svenpetersen1965/C64-Control-Port-Switch-Rapid-Fire-/case/rev 0/InkScape/decal.png

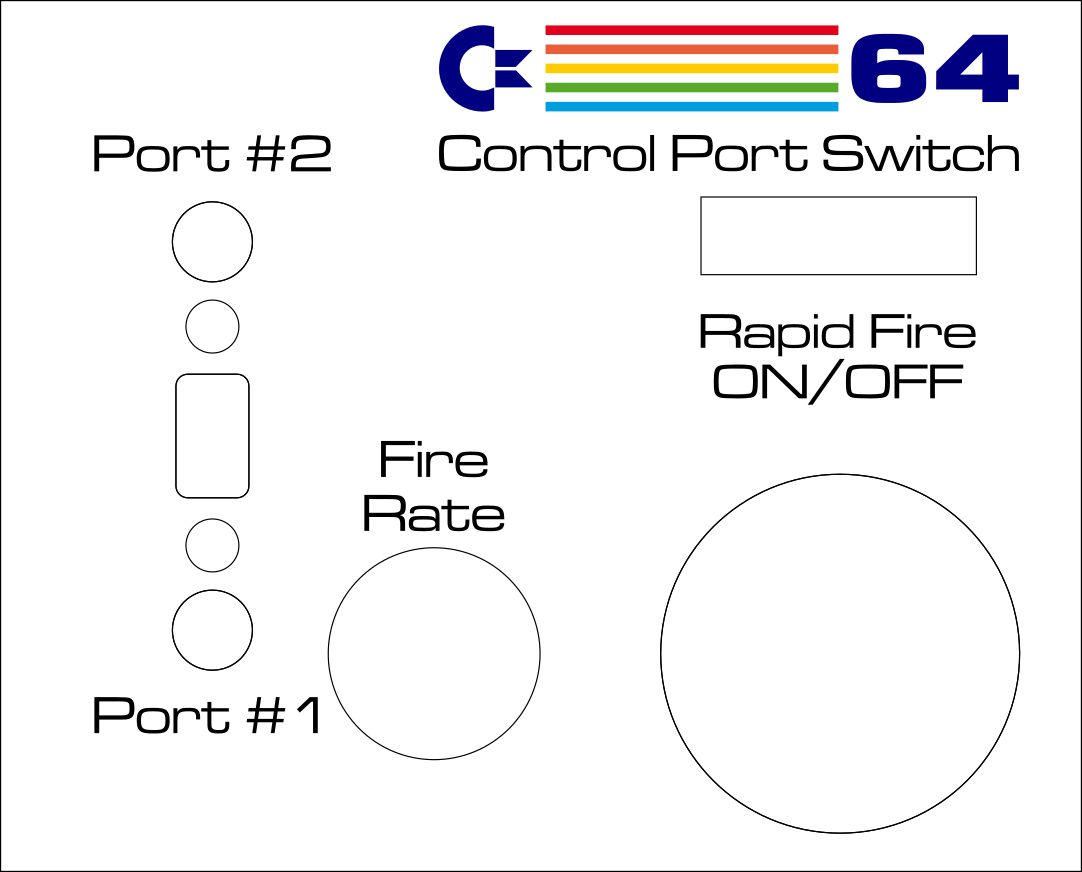
case/rev 0/InkScape/decal.png
