svenpetersen1965/C64-Control-Port-Switch-Rapid-Fire-/Hardware/Rev. 1/pictures/4124_-_display_cable.JPG

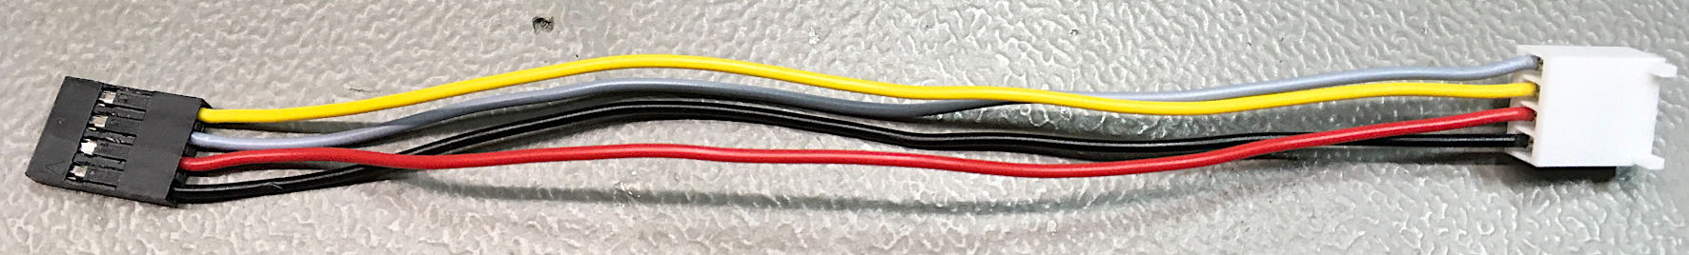
Hardware/Rev. 1/pictures/4124_-_display_cable.JPG
