svenpetersen1965/C64-Control-Port-Switch-Rapid-Fire-/Hardware/Rev. 1/pictures/4126_-_potentiometer_cable.JPG

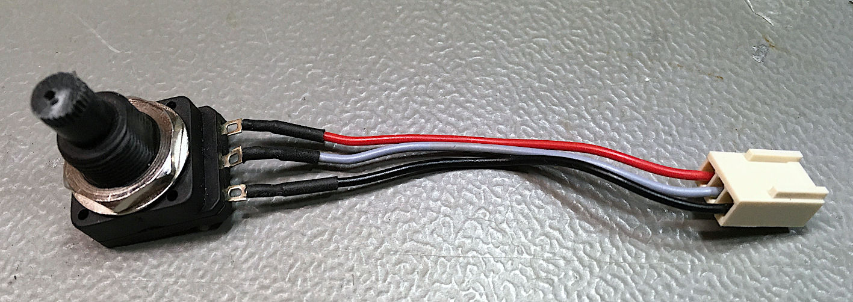
Hardware/Rev. 1/pictures/4126_-_potentiometer_cable.JPG
