svenpetersen1965/C64-Control-Port-Switch-Rapid-Fire-/Hardware/Rev. 1/pictures/4131_-_display.JPG

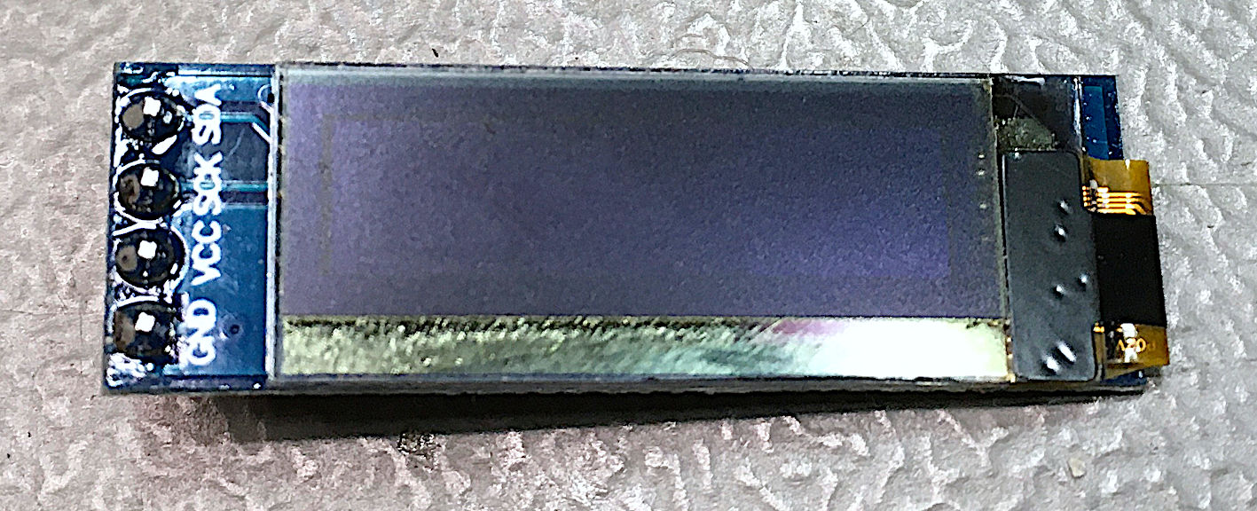
Hardware/Rev. 1/pictures/4131_-_display.JPG
