svenpetersen1965/C64-Control-Port-Switch-Rapid-Fire-/Hardware/Rev. 1/pictures/4147_-_wire_separated.JPG

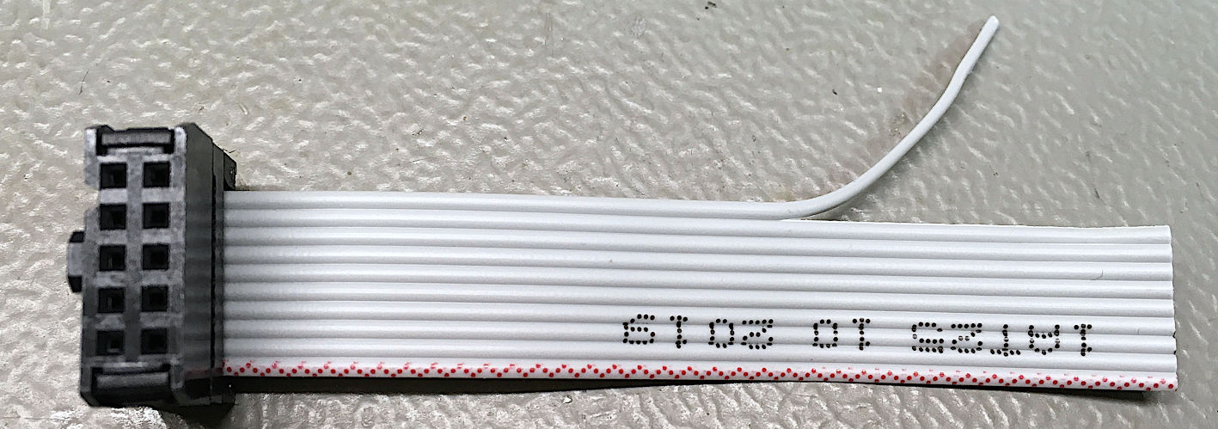
Hardware/Rev. 1/pictures/4147_-_wire_separated.JPG
