svenpetersen1965/C64-Control-Port-Switch-Rapid-Fire-/Hardware/Rev. 1/pictures/4148_-_Dsub_aligned.JPG

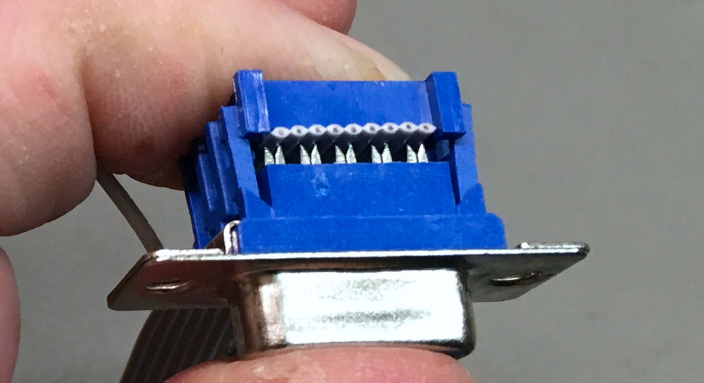
Hardware/Rev. 1/pictures/4148_-_Dsub_aligned.JPG
