svenpetersen1965/C64-Control-Port-Switch-Rapid-Fire-/Hardware/Rev. 1/pictures/4149_-_Dsub_wrench.JPG

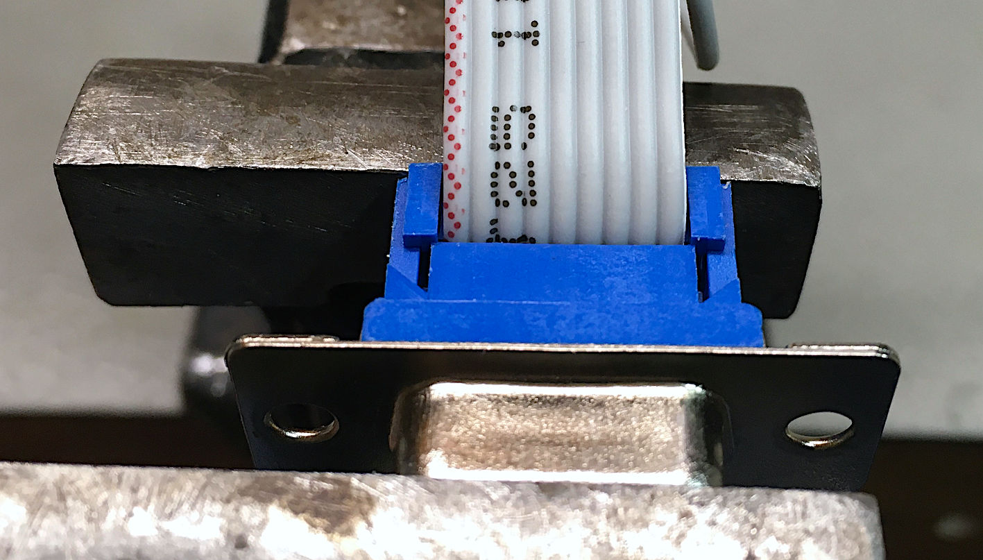
Hardware/Rev. 1/pictures/4149_-_Dsub_wrench.JPG
