svenpetersen1965/C64-Control-Port-Switch-Rapid-Fire-/Hardware/Rev. 1/pictures/ada_gfx.png

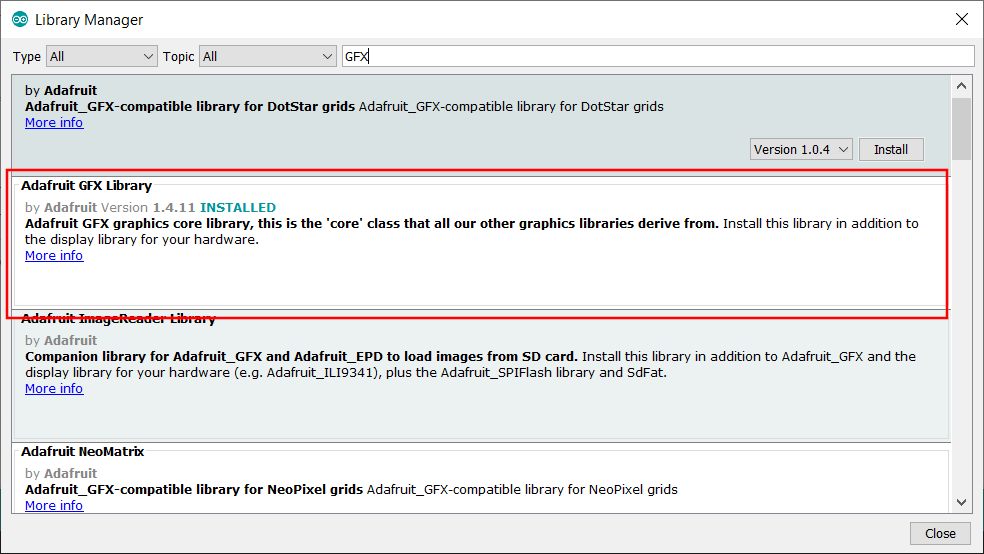
Hardware/Rev. 1/pictures/ada_gfx.png
