svenpetersen1965/C64-Control-Port-Switch-Rapid-Fire-/Hardware/Rev. 1/pictures/JSRF_+slope_out_100us.png

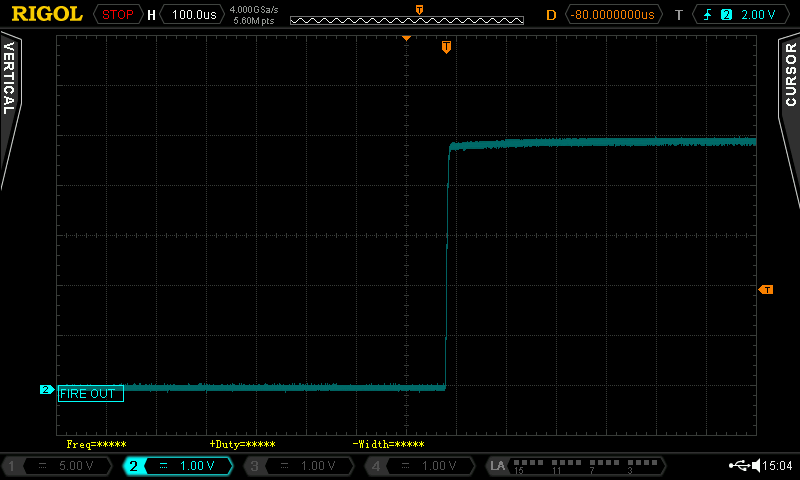
Hardware/Rev. 1/pictures/JSRF_+slope_out_100us.png
