svenpetersen1965/C64-Control-Port-Switch-Rapid-Fire-/Hardware/Rev. 1/pictures/JSRF_-slope_in_out_1ms.png

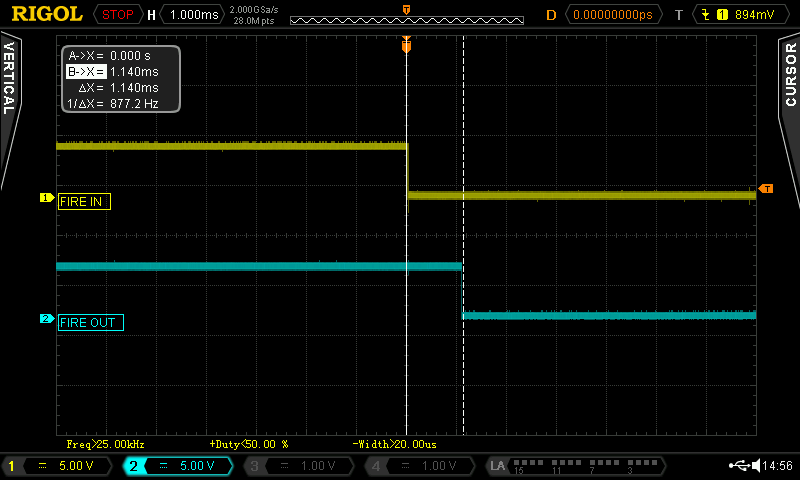
Hardware/Rev. 1/pictures/JSRF_-slope_in_out_1ms.png
