svenpetersen1965/C64-Control-Port-Switch-Rapid-Fire-/Hardware/Rev. 1/pictures/JSRF_out_50ms.png

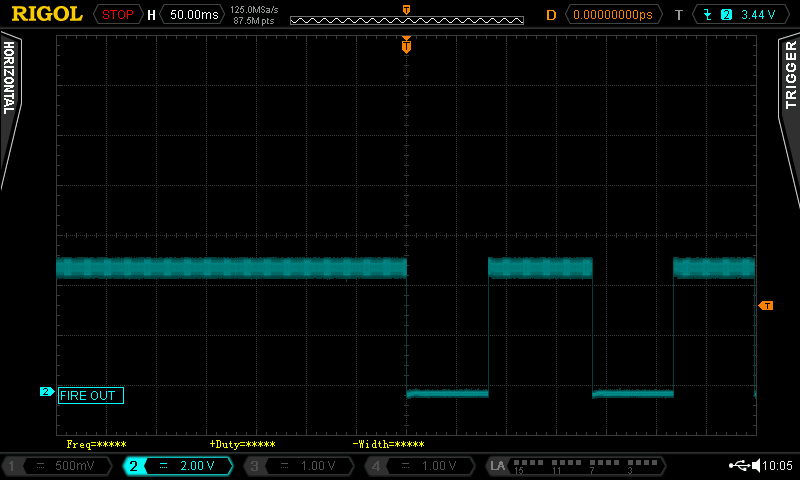
Hardware/Rev. 1/pictures/JSRF_out_50ms.png
