svenpetersen1965/C64-Control-Port-Switch-Rapid-Fire-/Hardware/Rev. 1/pictures/4134_-_pot_display_cbl_installed.JPG

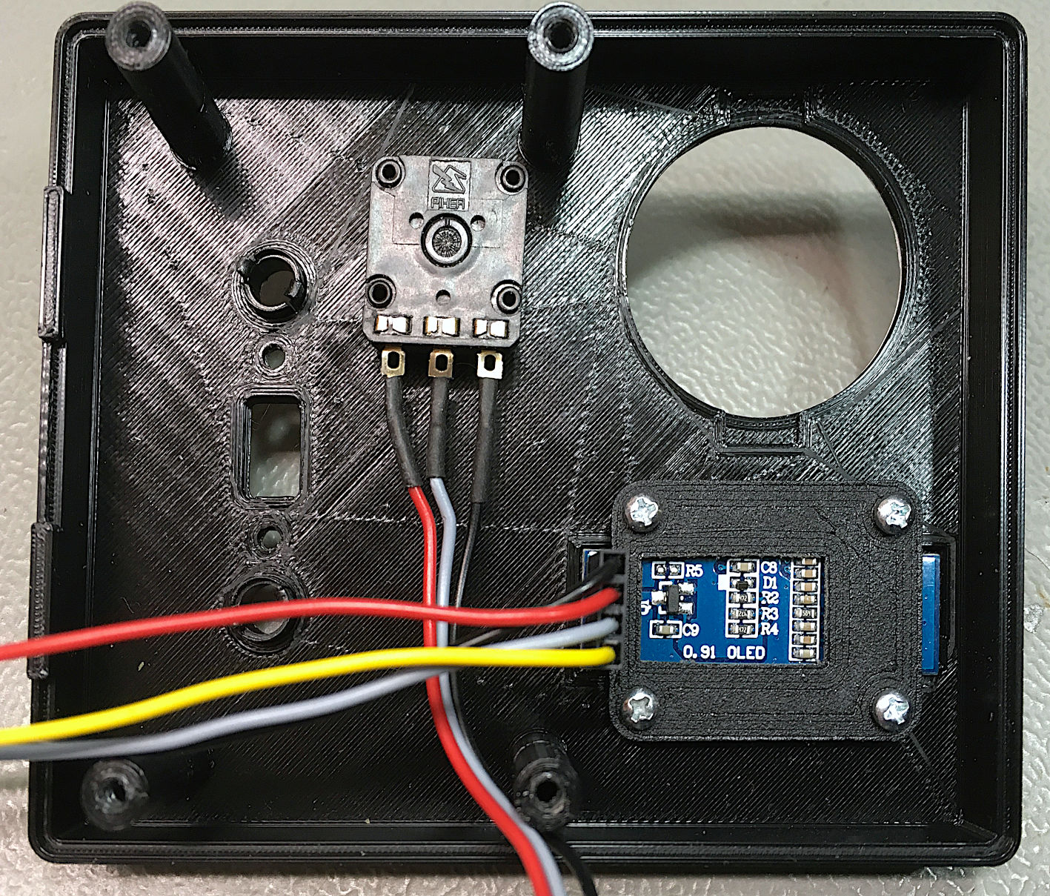
Hardware/Rev. 1/pictures/4134_-_pot_display_cbl_installed.JPG
