svenpetersen1965/C64-Control-Port-Switch-Rapid-Fire-/Hardware/Rev. 1/pictures/4138_-_bottom_installed.JPG

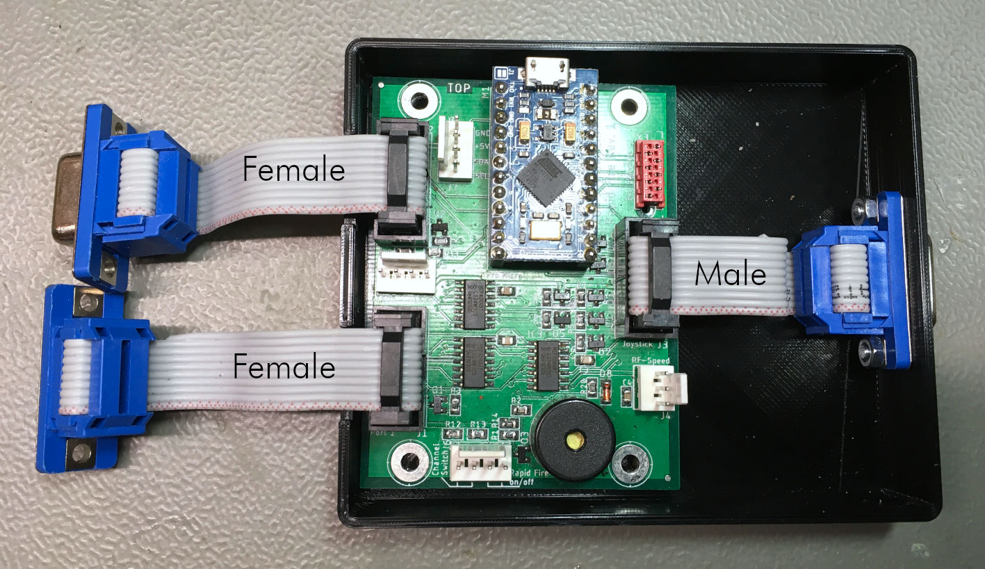
Hardware/Rev. 1/pictures/4138_-_bottom_installed.JPG
